ErikaB-sys/Fiddle_yard_UVB/FY_Controller_Motor/reports/misra.csv

lib\BabelFish\BabelFish.cpp | 38 | error | misra-config | Because of missing configuration | misra checking is incomplete. There can be false negatives! Variable 'Serial' is unknown
lib\BabelFish\BabelFish.cpp | 164 | error | misra-config | Because of missing configuration | misra checking is incomplete. There can be false negatives! Variable 'nullptr' is unknown
lib\BabelFish\BabelFish.cpp | 175 | error | misra-config | Because of missing configuration | misra checking is incomplete. There can be false negatives! Variable 'nullptr' is unknown
lib\BabelFish\BabelFish.cpp | 215 | error | misra-config | Because of missing configuration | misra checking is incomplete. There can be false negatives! Variable 'nullptr' is unknown
lib\BabelFish\BabelFish.cpp | 262 | error | misra-config | Because of missing configuration | misra checking is incomplete. There can be false negatives! Variable 'nullptr' is unknown
lib\BabelFish\BabelFish.cpp | 283 | error | misra-config | Because of missing configuration | misra checking is incomplete. There can be false negatives! Variable 'nullptr' is unknown
lib\BabelFish\BabelFish.cpp | 311 | error | misra-config | Because of missing configuration | misra checking is incomplete. There can be false negatives! Variable 'nullptr' is unknown
lib\BabelFish\BabelFish.cpp | 312 | error | misra-config | Because of missing configuration | misra checking is incomplete. There can be false negatives! Variable 'nullptr' is unknown
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
lib\UART\UART.cpp | 676 | error | misra-config | Because of missing configuration | misra checking is incomplete. There can be false negatives! Variable 'nullptr' is unknown
lib\UART\UART.cpp | 677 | error | misra-config | Because of missing configuration | misra checking is incomplete. There can be false negatives! Variable 'nullptr' is unknown
lib\UART\UART.cpp | 684 | error | misra-config | Because of missing configuration | misra checking is incomplete. There can be false negatives! Variable 'FY_SystemState_t' is unknown
