ErikaB-sys/Fiddle_yard_UVB/FY_Controller_Motor/reports/misra_full.csv

lib\BabelFish\BabelFish.cpp | 366 | style | functionStatic | The member function 'BabelFish::reportInvalid' can be static.
lib\BabelFish\BabelFish.cpp | 391 | style | constVariablePointer | Variable 'start' can be declared as pointer to const
lib\BabelFish\BabelFish.cpp | 38 | error | misra-config | Because of missing configuration | misra checking is incomplete. There can be false negatives! Variable 'Serial' is unknown
lib\BabelFish\BabelFish.cpp | 164 | error | misra-config | Because of missing configuration | misra checking is incomplete. There can be false negatives! Variable 'nullptr' is unknown
lib\BabelFish\BabelFish.cpp | 175 | error | misra-config | Because of missing configuration | misra checking is incomplete. There can be false negatives! Variable 'nullptr' is unknown
lib\BabelFish\BabelFish.cpp | 215 | error | misra-config | Because of missing configuration | misra checking is incomplete. There can be false negatives! Variable 'nullptr' is unknown
lib\BabelFish\BabelFish.cpp | 262 | error | misra-config | Because of missing configuration | misra checking is incomplete. There can be false negatives! Variable 'nullptr' is unknown
lib\BabelFish\BabelFish.cpp | 283 | error | misra-config | Because of missing configuration | misra checking is incomplete. There can be false negatives! Variable 'nullptr' is unknown
lib\BabelFish\BabelFish.cpp | 311 | error | misra-config | Because of missing configuration | misra checking is incomplete. There can be false negatives! Variable 'nullptr' is unknown
lib\BabelFish\BabelFish.cpp | 312 | error | misra-config | Because of missing configuration | misra checking is incomplete. There can be false negatives! Variable 'nullptr' is unknown
lib\BabelFish\BabelFish.cpp | 443 | error | misra-config | Because of missing configuration | misra checking is incomplete. There can be false negatives! Variable 'nullptr' is unknown
lib\BabelFish\BabelFish.cpp | 480 | error | misra-config | Because of missing configuration | misra checking is incomplete. There can be false negatives! Variable 'nullptr' is unknown
lib\BabelFish\BabelFish.cpp | 504 | error | misra-config | Because of missing configuration | misra checking is incomplete. There can be false negatives! Variable 'nullptr' is unknown
lib\Error\Error.cpp | 18 | style | functionStatic | The member function 'Error::update' can be static.
lib\Keyboard\Keyboard.cpp | 5 | warning | uninitMemberVar | Member variable 'Button::_lastState' is not initialized in the constructor.
lib\Keyboard\Keyboard.cpp | 256 | style | unusedPrivateFunction | Unused private function: 'Keyboard::drawDiagnostic'
lib\Keyboard\Keyboard.cpp | 282 | style | functionStatic | The member function 'Keyboard::Write_to_display' can be static.
lib\Keyboard\Keyboard.cpp | 256 | style | functionStatic | The member function 'Keyboard::drawDiagnostic' can be static.
lib\Keyboard\Keyboard.cpp | 146 | style | shadowFunction | Argument 'mode' shadows outer function
lib\Keyboard\Keyboard.cpp | 28 | error | misra-config | Because of missing configuration | misra checking is incomplete. There can be false negatives! Variable 'HIGH' is unknown
lib\Keyboard\Keyboard.cpp | 28 | error | misra-config | Because of missing configuration | misra checking is incomplete. There can be false negatives! Variable 'LOW' is unknown
lib\Motor\motor.cpp | 63 | warning | uninitMemberVar | Member variable 'Motor::_Dir_pin' is not initialized in the constructor.
lib\Motor\motor.cpp | 63 | warning | uninitMemberVar | Member variable 'Motor::_Step_pin' is not initialized in the constructor.
lib\Motor\motor.cpp | 63 | warning | uninitMemberVar | Member variable 'Motor::_ENA_pin' is not initialized in the constructor.
lib\Motor\motor.cpp | 63 | warning | uninitMemberVar | Member variable 'Motor::_State' is not initialized in the constructor.
lib\Motor\motor.cpp | 63 | warning | uninitMemberVar | Member variable 'Motor::_ProfileElement' is not initialized in the constructor.
lib\Motor\motor.cpp | 63 | warning | uninitMemberVar | Member variable 'Motor::_TargetPosition' is not initialized in the constructor.
lib\Motor\motor.cpp | 63 | warning | uninitMemberVar | Member variable 'Motor::_Position' is not initialized in the constructor.
lib\Motor\motor.cpp | 352 | style | unusedPrivateFunction | Unused private function: 'Motor::CheckBorder'
lib\Motor\motor.cpp | 408 | style | unusedPrivateFunction | Unused private function: 'Motor::calcProfile'
lib\Motor\motor.cpp | 525 | style | unusedPrivateFunction | Unused private function: 'Motor::Timer1_Start'
lib\Motor\motor.cpp | 218 | style | functionStatic | The member function 'Motor::move2Pos' can be static.
lib\Motor\motor.cpp | 228 | style | functionStatic | The member function 'Motor::moveSteps' can be static.
lib\Motor\motor.cpp | 305 | style | functionStatic | The member function 'Motor::Reference' can be static.
lib\Motor\motor.cpp | 319 | style | functionStatic | The member function 'Motor::prepareSetPosition' can be static.
lib\Motor\motor.cpp | 327 | style | functionStatic | The member function 'Motor::prepareLeft' can be static.
lib\Motor\motor.cpp | 335 | style | functionStatic | The member function 'Motor::prepareRight' can be static.
lib\Motor\motor.cpp | 343 | style | functionStatic | The member function 'Motor::prepareSetTrack' can be static.
lib\Motor\motor.cpp | 352 | style | functionStatic | The member function 'Motor::CheckBorder' can be static.
lib\Motor\motor.cpp | 357 | style | functionStatic | The member function 'Motor::prepareParameter' can be static.
lib\Motor\motor.cpp | 585 | style | functionStatic | The member function 'Motor::Timer1_Stop' can be static.
lib\Motor\motor.cpp | 150 | style | knownConditionTrueFalse | Condition 'true==prepareLeft()' is always true
lib\Motor\motor.cpp | 157 | style | knownConditionTrueFalse | Condition 'true==prepareRight()' is always true
lib\Motor\motor.cpp | 164 | style | knownConditionTrueFalse | Condition 'true==prepareSetPosition()' is always true
lib\Motor\motor.cpp | 171 | style | knownConditionTrueFalse | Condition 'true==prepareSetTrack()' is always true
lib\Motor\motor.cpp | 178 | style | knownConditionTrueFalse | Condition 'true==prepareParameter()' is always true
lib\Motor\motor.cpp | 191 | style | knownConditionTrueFalse | Condition 'prepareParameter()' is always true
lib\Motor\motor.cpp | 248 | style | useStlAlgorithm | Consider using std::find_if algorithm instead of a raw loop.
lib\Motor\motor.cpp | 91 | error | misra-config | Because of missing configuration | misra checking is incomplete. There can be false negatives! Variable 'nullptr' is unknown
lib\Motor\motor.cpp | 240 | error | misra-config | Because of missing configuration | misra checking is incomplete. There can be false negatives! Variable 'MotorState_t' is unknown
lib\Motor\motor.cpp | 254 | error | misra-config | Because of missing configuration | misra checking is incomplete. There can be false negatives! Variable 'nullptr' is unknown
lib\Motor\motor.cpp | 258 | error | misra-config | Because of missing configuration | misra checking is incomplete. There can be false negatives! Variable 'REF_STATE' is unknown
lib\Motor\motor.cpp | 279 | error | misra-config | Because of missing configuration | misra checking is incomplete. There can be false negatives! Variable 'nullptr' is unknown
lib\Motor\motor.cpp | 292 | error | misra-config | Because of missing configuration | misra checking is incomplete. There can be false negatives! Variable 'nullptr' is unknown
lib\Motor\motor.cpp | 630 | error | misra-config | Because of missing configuration | misra checking is incomplete. There can be false negatives! Variable 'nullptr' is unknown
lib\Motor\motor.cpp | 639 | error | misra-config | Because of missing configuration | misra checking is incomplete. There can be false negatives! Variable 'nullptr' is unknown
lib\Motor\motor.cpp | 677 | error | misra-config | Because of missing configuration | misra checking is incomplete. There can be false negatives! Variable 'nullptr' is unknown
lib\Motor\motor.cpp | 684 | error | misra-config | Because of missing configuration | misra checking is incomplete. There can be false negatives! Variable 'nullptr' is unknown
lib\Motor\motor.cpp | 804 | error | misra-config | Because of missing configuration | misra checking is incomplete. There can be false negatives! Variable 'MotorProfile_t' is unknown
lib\Motor\motor.cpp | 818 | error | misra-config | Because of missing configuration | misra checking is incomplete. There can be false negatives! Variable 'nullptr' is unknown
lib\Switches\Switches.cpp | 3 | style | functionStatic | The member function 'Switches::begin' can be static.
lib\Switches\Switches.cpp | 11 | style | functionStatic | The member function 'Switches::getAnalogValue' can be static.
lib\Switches\Switches.cpp | 22 | style | functionStatic | The member function 'Switches::getDigitalValue' can be static.
lib\UART\UART.cpp | 325 | style | unusedPrivateFunction | Unused private function: 'UART::sendNack'
lib\UART\UART.cpp | 379 | style | unusedPrivateFunction | Unused private function: 'UART::CheckError'
lib\UART\UART.cpp | 374 | style | unusedPrivateFunction | Unused private function: 'UART::CheckBusy'
lib\UART\UART.cpp | 621 | style | unusedPrivateFunction | Unused private function: 'UART::handle_ACK'
lib\UART\UART.cpp | 17 | performance | useInitializationList | Variable 'CommandBuffer' is assigned in constructor body. Consider performing initialization in initialization list.
lib\UART\UART.cpp | 20 | performance | useInitializationList | Variable 'ResponseBuffer' is assigned in constructor body. Consider performing initialization in initialization list.
lib\UART\UART.cpp | 379 | style | functionStatic | The member function 'UART::CheckError' can be static.
lib\UART\UART.cpp | 374 | style | functionStatic | The member function 'UART::CheckBusy' can be static.
lib\UART\UART.cpp | 399 | style | functionStatic | The member function 'UART::Calc_CRC' can be static.
lib\UART\UART.cpp | 419 | style | functionStatic | The member function 'UART::Calc_CRC_PGM' can be static.
lib\UART\UART.cpp | 332 | style | functionStatic | The member function 'UART::sendHello' can be static.
lib\UART\UART.cpp | 38 | error | misra-config | Because of missing configuration | misra checking is incomplete. There can be false negatives! Variable 'nullptr' is unknown
lib\UART\UART.cpp | 72 | error | misra-config | Because of missing configuration | misra checking is incomplete. There can be false negatives! Variable 'Serial' is unknown
lib\UART\UART.cpp | 79 | error | misra-config | Because of missing configuration | misra checking is incomplete. There can be false negatives! Variable 'BabelFishResult' is unknown
lib\UART\UART.cpp | 114 | error | misra-config | Because of missing configuration | misra checking is incomplete. There can be false negatives! Variable 'BabelFishResult' is unknown
lib\UART\UART.cpp | 146 | error | misra-config | Because of missing configuration | misra checking is incomplete. There can be false negatives! Variable 'static_cast' is unknown
lib\UART\UART.cpp | 226 | error | misra-config | Because of missing configuration | misra checking is incomplete. There can be false negatives! Variable 'FY_SystemState_t' is unknown
lib\UART\UART.cpp | 293 | error | misra-config | Because of missing configuration | misra checking is incomplete. There can be false negatives! Variable 'ResponseContainer' is unknown
lib\UART\UART.cpp | 339 | error | misra-config | Because of missing configuration | misra checking is incomplete. There can be false negatives! Variable 'nullptr' is unknown
lib\UART\UART.cpp | 345 | error | misra-config | Because of missing configuration | misra checking is incomplete. There can be false negatives! Variable 'nullptr' is unknown
lib\UART\UART.cpp | 388 | error | misra-config | Because of missing configuration | misra checking is incomplete. There can be false negatives! Variable 'nullptr' is unknown
lib\UART\UART.cpp | 461 | error | misra-config | Because of missing configuration | misra checking is incomplete. There can be false negatives! Variable 'nullptr' is unknown
lib\UART\UART.cpp | 488 | error | misra-config | Because of missing configuration | misra checking is incomplete. There can be false negatives! Variable 'nullptr' is unknown
lib\UART\UART.cpp | 500 | error | misra-config | Because of missing configuration | misra checking is incomplete. There can be false negatives! Variable 'nullptr' is unknown
lib\UART\UART.cpp | 534 | error | misra-config | Because of missing configuration | misra checking is incomplete. There can be false negatives! Variable 'nullptr' is unknown
lib\UART\UART.cpp | 568 | error | misra-config | Because of missing configuration | misra checking is incomplete. There can be false negatives! Variable 'nullptr' is unknown
lib\UART\UART.cpp | 569 | error | misra-config | Because of missing configuration | misra checking is incomplete. There can be false negatives! Variable 'nullptr' is unknown
lib\UART\UART.cpp | 570 | error | misra-config | Because of missing configuration | misra checking is incomplete. There can be false negatives! Variable 'nullptr' is unknown
lib\UART\UART.cpp | 577 | error | misra-config | Because of missing configuration | misra checking is incomplete. There can be false negatives! Variable 'FY_SystemState_t' is unknown
lib\UART\UART.cpp | 583 | error | misra-config | Because of missing configuration | misra checking is incomplete. There can be false negatives! Variable 'nullptr' is unknown
lib\UART\UART.cpp | 584 | error | misra-config | Because of missing configuration | misra checking is incomplete. There can be false negatives! Variable 'nullptr' is unknown
lib\UART\UART.cpp | 661 | error | misra-config | Because of missing configuration | misra checking is incomplete. There can be false negatives! Variable 'static_cast' is unknown
lib\UART\UART.cpp | 662 | error | misra-config | Because of missing configuration | misra checking is incomplete. There can be false negatives! Variable 'static_cast' is unknown
lib\UART\UART.cpp | 675 | error | misra-config | Because of missing configuration | misra checking is incomplete. There can be false negatives! Variable 'nullptr' is unknown
lib\UART\UART.cpp | 676 | error | misra-config | Because of missing configuration | misra checking is incomplete. There can be false negatives! Variable 'nullptr' is unknown
lib\UART\UART.cpp | 677 | error | misra-config | Because of missing configuration | misra checking is incomplete. There can be false negatives! Variable 'nullptr' is unknown
lib\UART\UART.cpp | 684 | error | misra-config | Because of missing configuration | misra checking is incomplete. There can be false negatives! Variable 'FY_SystemState_t' is unknown
