ErikaB-sys/Fiddle_yard_UVB/Documents/Pictures/K1600/1000129825.JPG

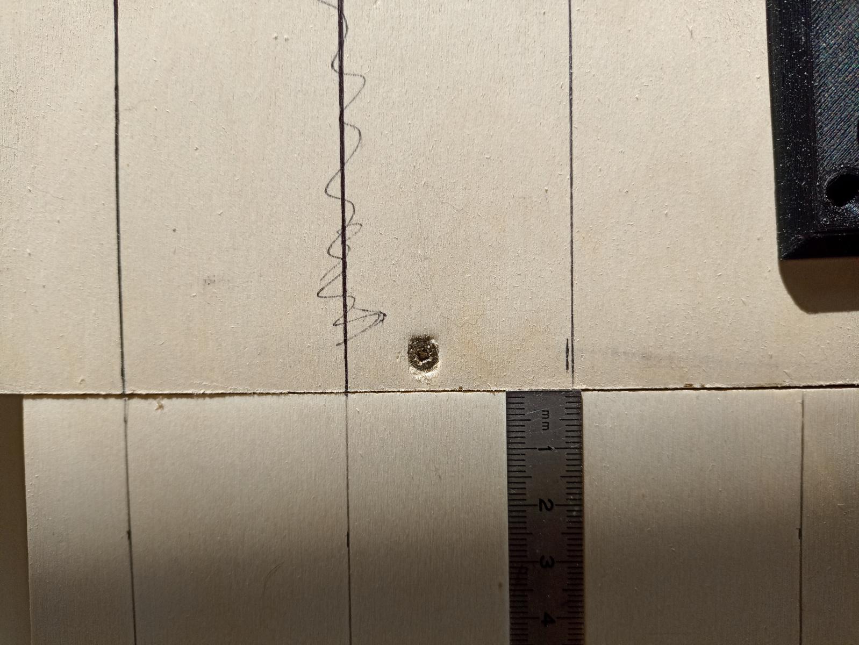
Documents/Pictures/K1600/1000129825.JPG
