ErikaB-sys/Fiddle_yard_UVB/Parts/Schiebebbühne/Arduino_Gehäuse/Arduino_gehäuse-Unterteil.3mf

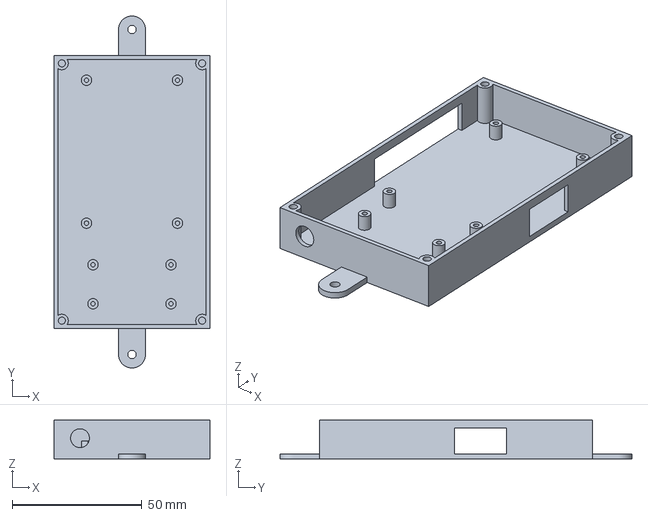
[picture p23: CAD file, 2026-09-12]
Parts/Schiebebbühne/Arduino_Gehäuse/Arduino_gehäuse-Unterteil.3mf
60.0 x 135.4 x 15.0 mm
