ErikaB-sys/Fiddle_yard_UVB/Parts/Schiebebbühne/Rolle/Rollenhalter-Chamfer001.3mf

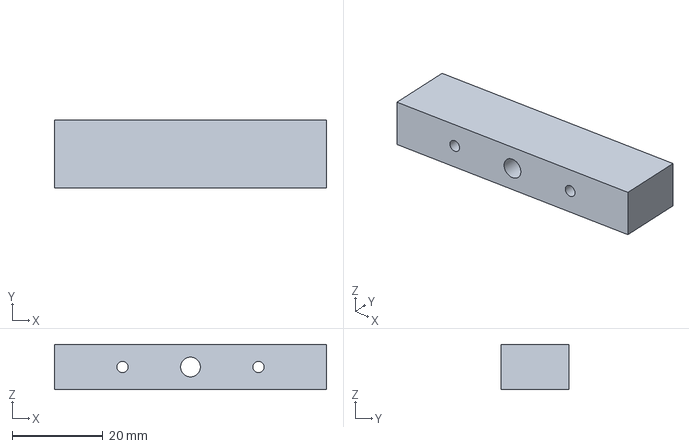
[picture p24: CAD file, 2026-09-14]
Parts/Schiebebbühne/Rolle/Rollenhalter-Chamfer001.3mf
60.0 x 15.0 x 10.0 mm
