ErikaB-sys/Fiddle_yard_UVB/Parts/Schiebebbühne/Rolle/Rollenhalter-Spanner.3mf

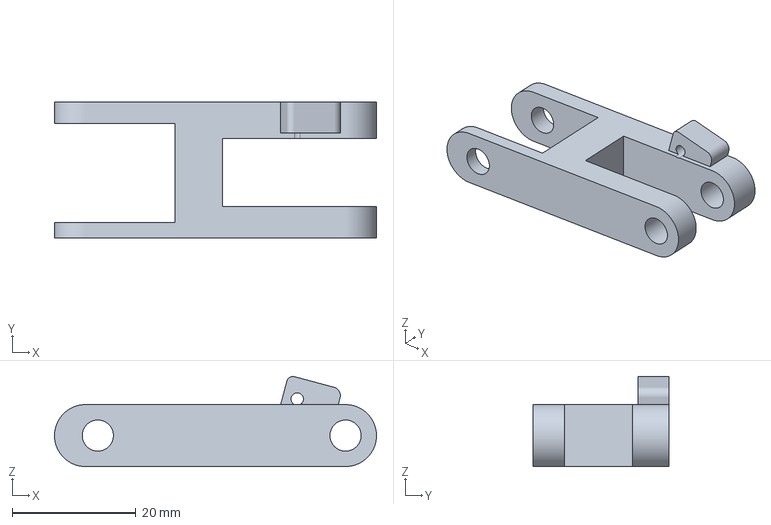
[picture p25: CAD file, 2026-09-14]
Parts/Schiebebbühne/Rolle/Rollenhalter-Spanner.3mf
52.0 x 22.0 x 14.5 mm
