ErikaB-sys/Fiddle_yard_UVB/Parts/Schiebebbühne/Rolle/Motorhalter.FCStd

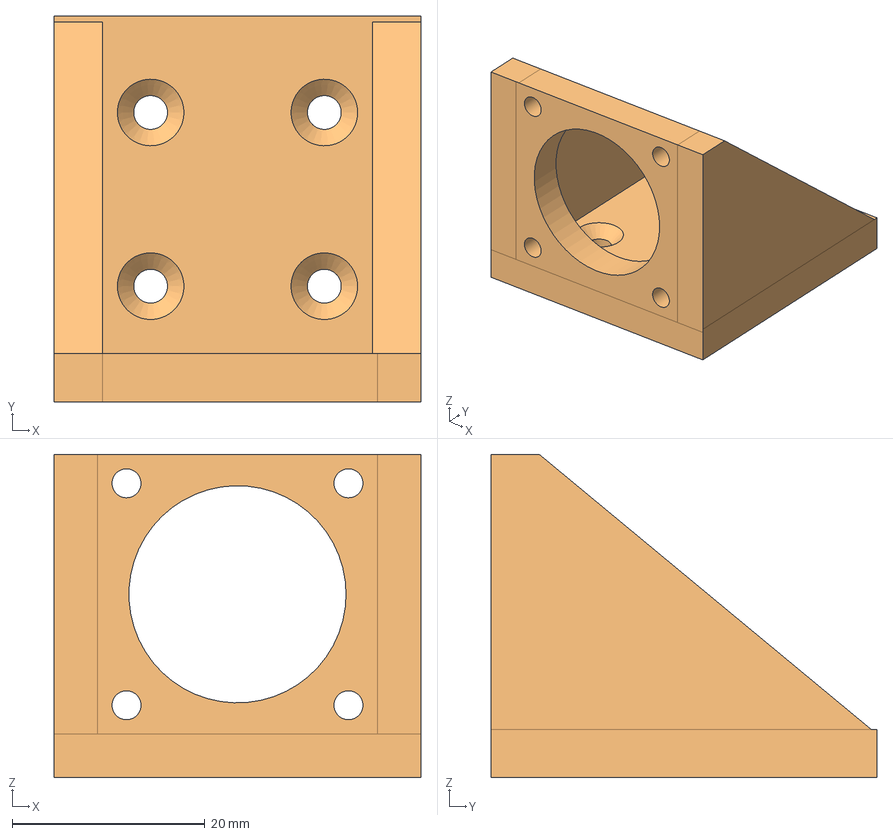
[picture p26: CAD file, 2026-09-14]
Parts/Schiebebbühne/Rolle/Motorhalter.FCStd
38.0 x 40.0 x 33.5 mm
Bodenplatte
