ErikaB-sys/Fiddle_yard_UVB/Parts/Schiebebbühne/Rolle/Motorhalter-Compound.stl

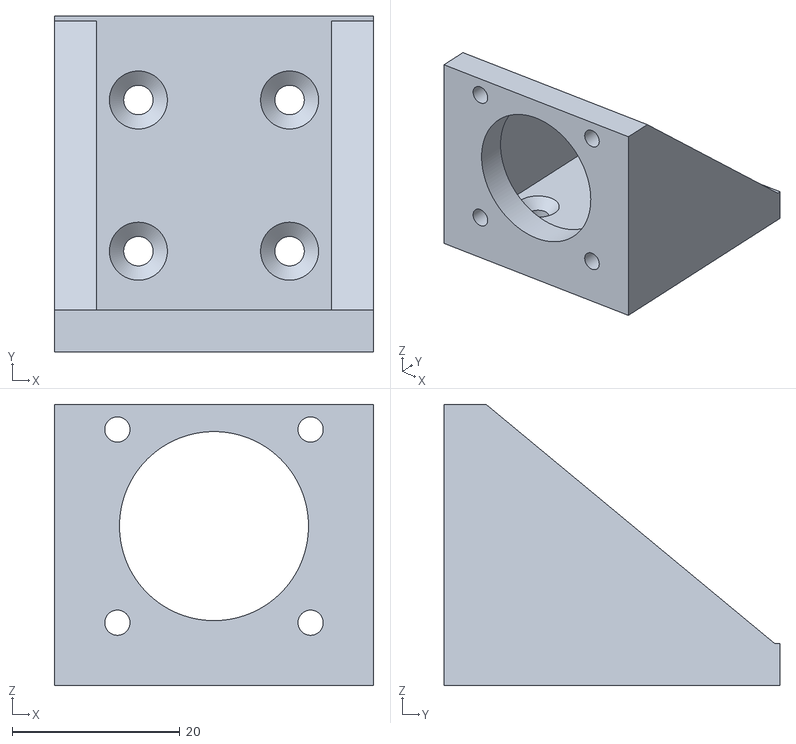
[picture p27: CAD file, 2026-09-14]
Parts/Schiebebbühne/Rolle/Motorhalter-Compound.stl
38.0 x 40.0 x 33.5
